tspspi/temparts/mirrors/parameterized_parabolic/manufacturedVariants/20231116_ParabolicScrewmount_003.png

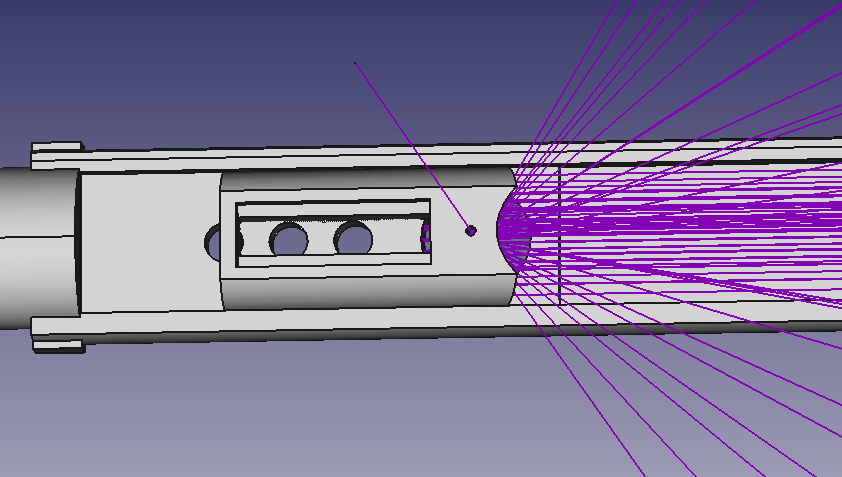
mirrors/parameterized_parabolic/manufacturedVariants/20231116_ParabolicScrewmount_003.png
