tspspi/temparts/mirrors/parameterized_parabolic/manufacturedVariants/20231129_changedParabolicScrewmount_002.png

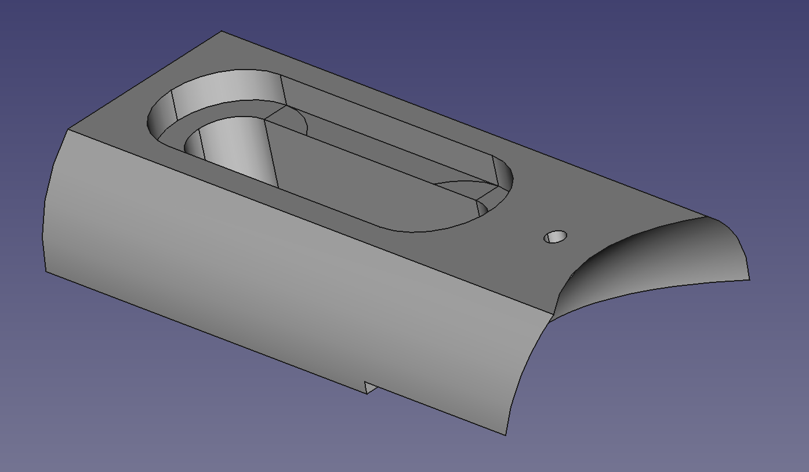
mirrors/parameterized_parabolic/manufacturedVariants/20231129_changedParabolicScrewmount_002.png
